sharebrained/medusa/hdl/medusa_cape/gamma.v

// Verilog asynchronous look-up table for LED brightness / gamma correction.

// Copyright (c) 2013 Jared Boone, ShareBrained Technology, Inc.
//
// This file is part of the Medusa project.
//
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

module gamma (
	input	[7:0]	v_i,
	output	reg	[7:0]	v_o
);

always @(v_i) begin
	case(v_i)
	0: v_o = 0;
	1: v_o = 1;
	2: v_o = 1;
	3: v_o = 1;
	4: v_o = 1;
	5: v_o = 1;
	6: v_o = 1;
	7: v_o = 1;
	8: v_o = 1;
	9: v_o = 1;
	10: v_o = 1;
	11: v_o = 1;
	12: v_o = 1;
	13: v_o = 1;
	14: v_o = 1;
	15: v_o = 1;
	16: v_o = 1;
	17: v_o = 1;
	18: v_o = 1;
	19: v_o = 1;
	20: v_o = 1;
	21: v_o = 1;
	22: v_o = 1;
	23: v_o = 1;
	24: v_o = 1;
	25: v_o = 1;
	26: v_o = 1;
	27: v_o = 1;
	28: v_o = 1;
	29: v_o = 1;
	30: v_o = 1;
	31: v_o = 1;
	32: v_o = 1;
	33: v_o = 2;
	34: v_o = 2;
	35: v_o = 2;
	36: v_o = 2;
	37: v_o = 2;
	38: v_o = 2;
	39: v_o = 2;
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
	default: v_o = 0;
	endcase
end

endmodule
